analoghifi/Thel-VX-preamp/VX-D/docs/german/VXDNF.png

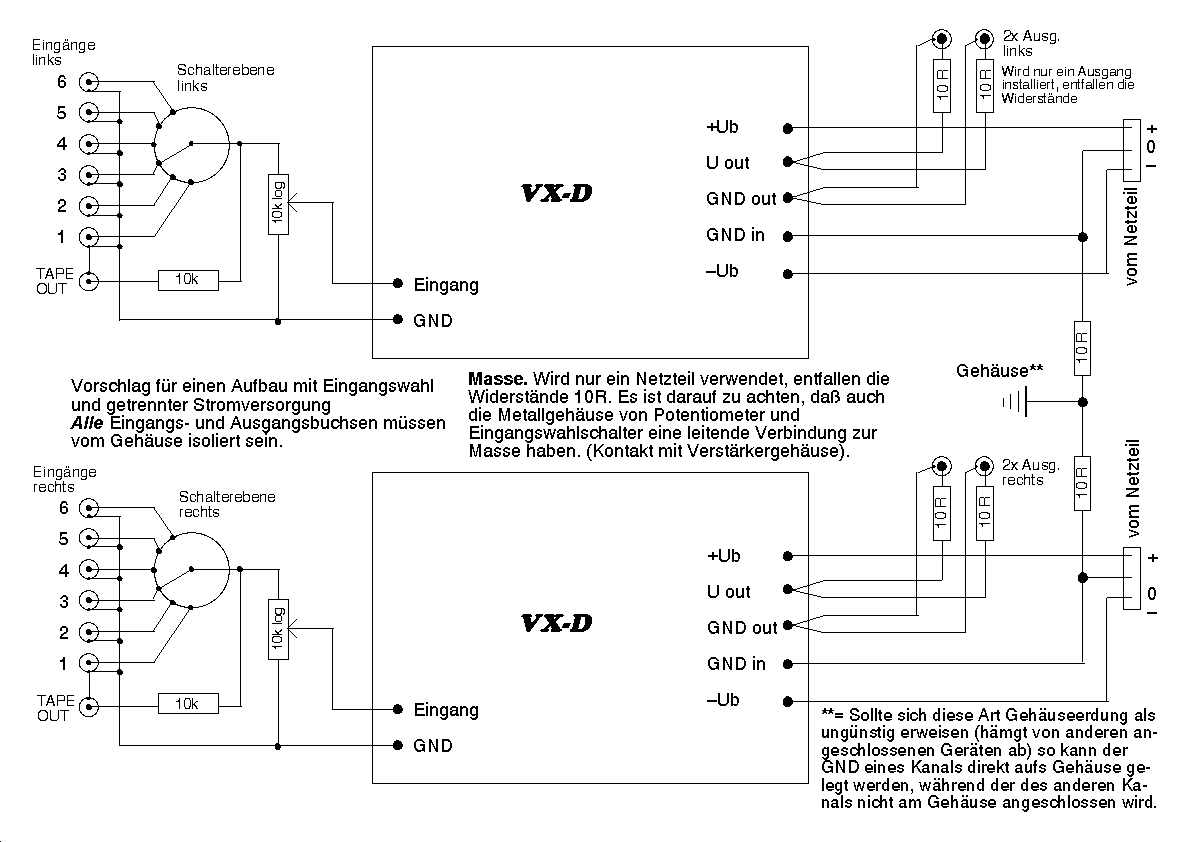
VX-D/docs/german/VXDNF.png
