analoghifi/Thel-VX-preamp/VX-D/hardware/VX-D_2.jpg

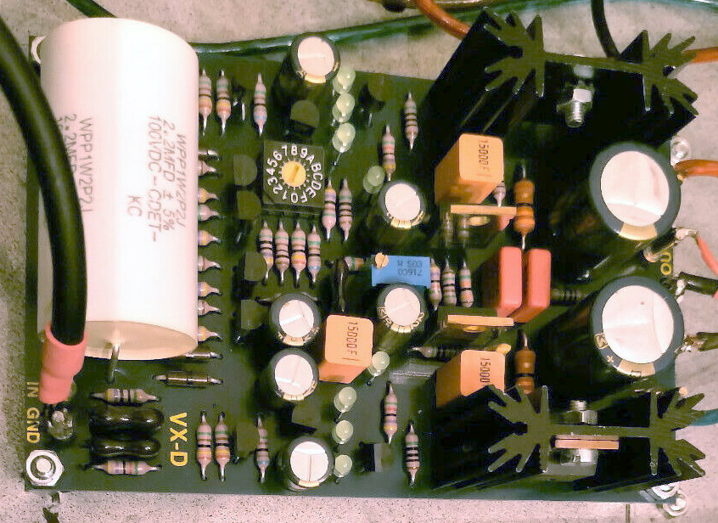
VX-D/hardware/VX-D_2.jpg
