analoghifi/Thel-VX-preamp/VX-D/hardware/VX-D_later_exemplar_1.jpg

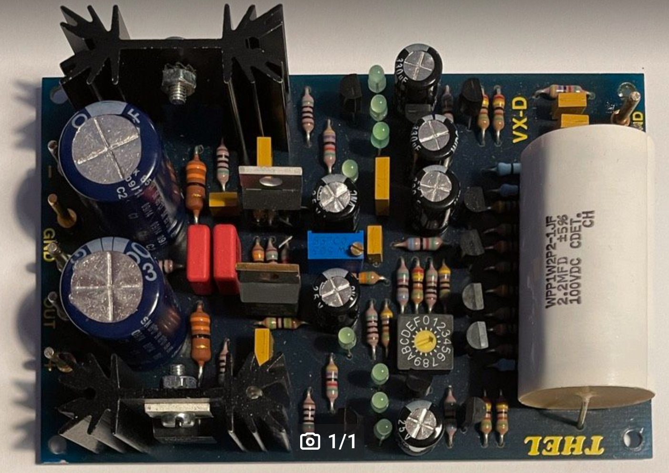
VX-D/hardware/VX-D_later_exemplar_1.jpg
