analoghifi/Thel-VX-preamp/VX-D/hardware/VX-D_later_exemplar_2.jpg

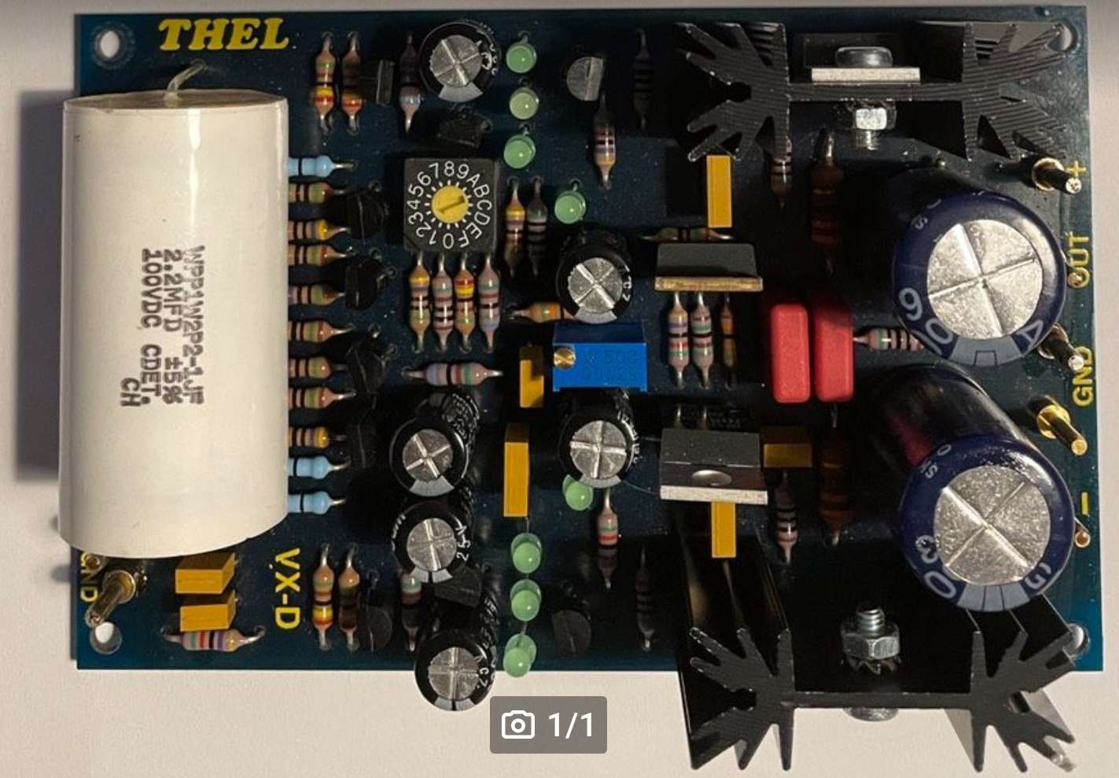
VX-D/hardware/VX-D_later_exemplar_2.jpg
