analoghifi/Thel-VX-preamp/VX-D/hardware/VX-D_Schematic_corr.jpg

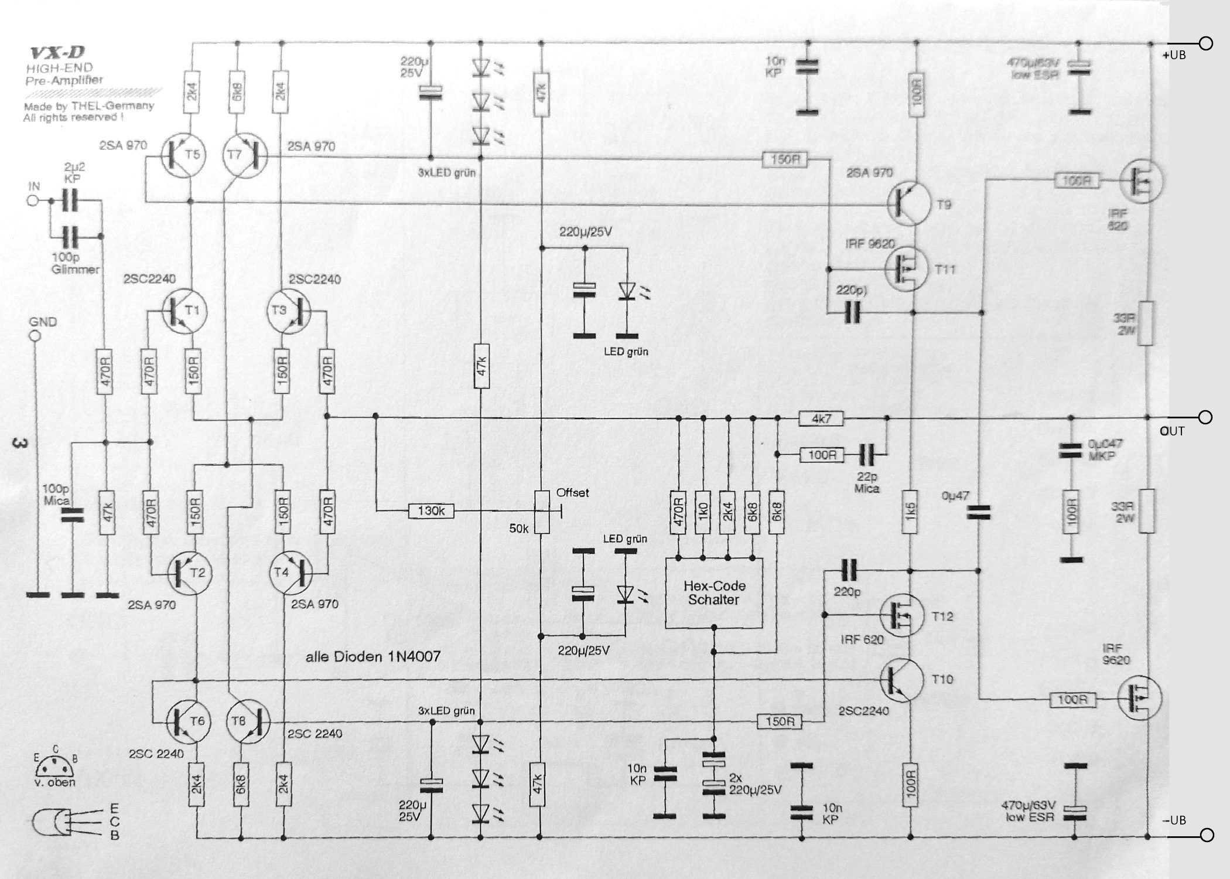
VX-D/hardware/VX-D_Schematic_corr.jpg
