analoghifi/Thel-VX-preamp/VX-Line/docs/german/VX-L1.png

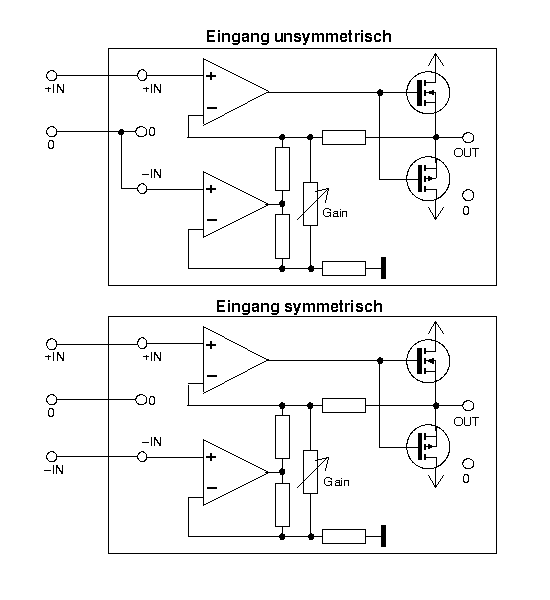
VX-Line/docs/german/VX-L1.png
