analoghifi/Thel-VX-preamp/VX-Line/docs/german/VX-L2.png

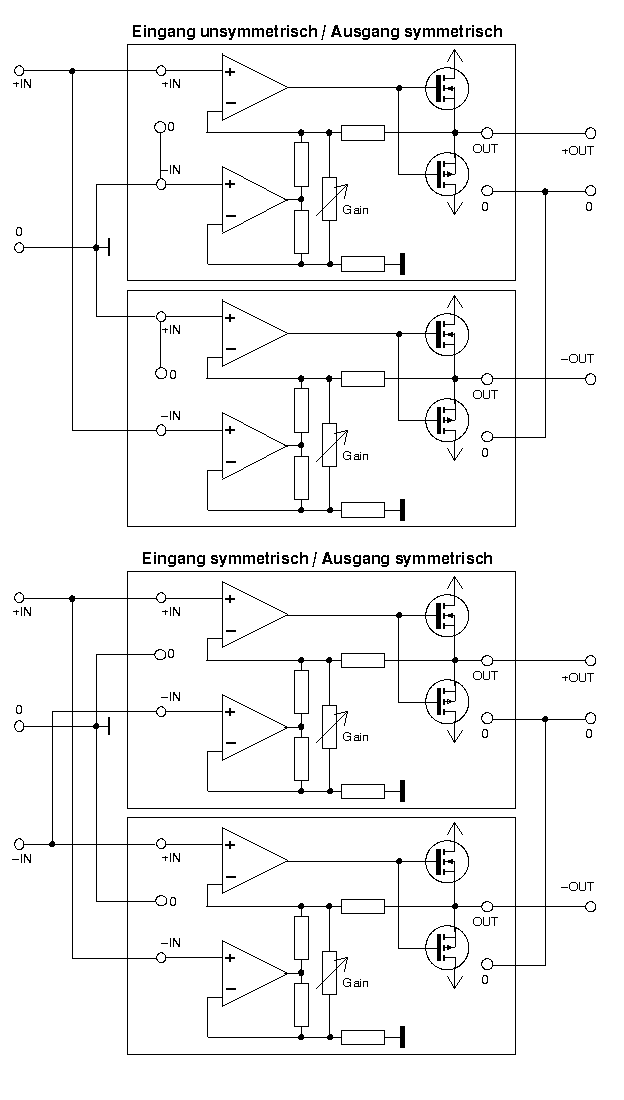
VX-Line/docs/german/VX-L2.png
