analoghifi/Thel-VX-preamp/VX-Line/hardware/KiCad/VX-Line_2021__original/VX-Line_original_1Layer_THT.sch.png

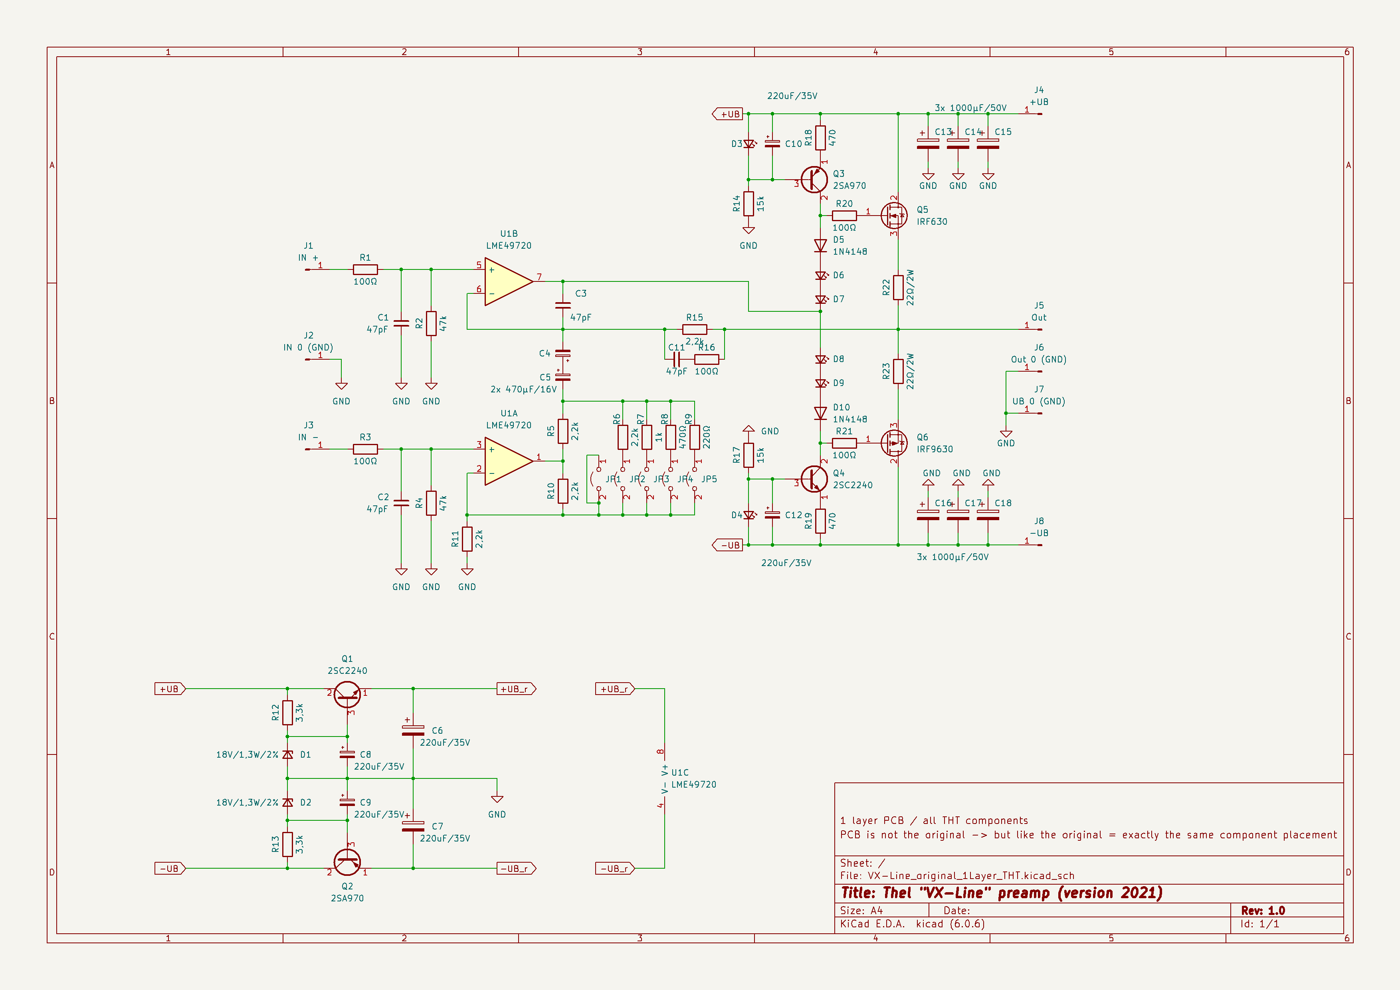
VX-Line/hardware/KiCad/VX-Line_2021__original/VX-Line_original_1Layer_THT.sch.png
