analoghifi/Thel-VX-preamp/VX-Line/hardware/KiCad/VX-Line_2021__original/VX-Line_original_1Layer_THT__3D_2.png

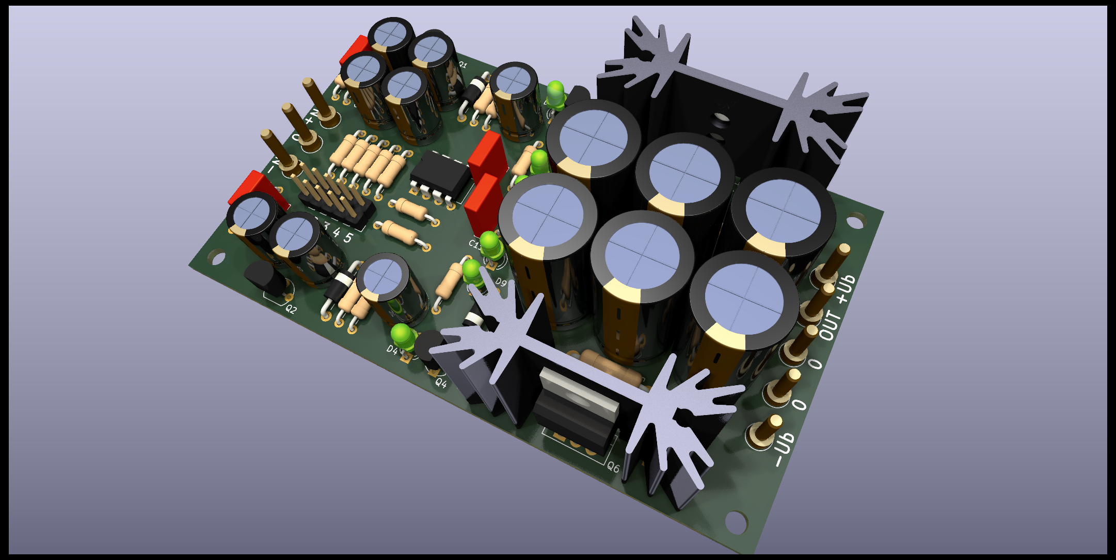
VX-Line/hardware/KiCad/VX-Line_2021__original/VX-Line_original_1Layer_THT__3D_2.png
