analoghifi/Thel-VX-preamp/VX-Line/hardware/VX-Line_2017-2020.jpg

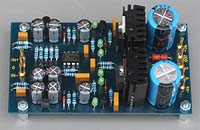
VX-Line/hardware/VX-Line_2017-2020.jpg
