analoghifi/Thel-VX-preamp/VX-Line/hardware/VX-Line_2021-PCB_Bottom.jpg

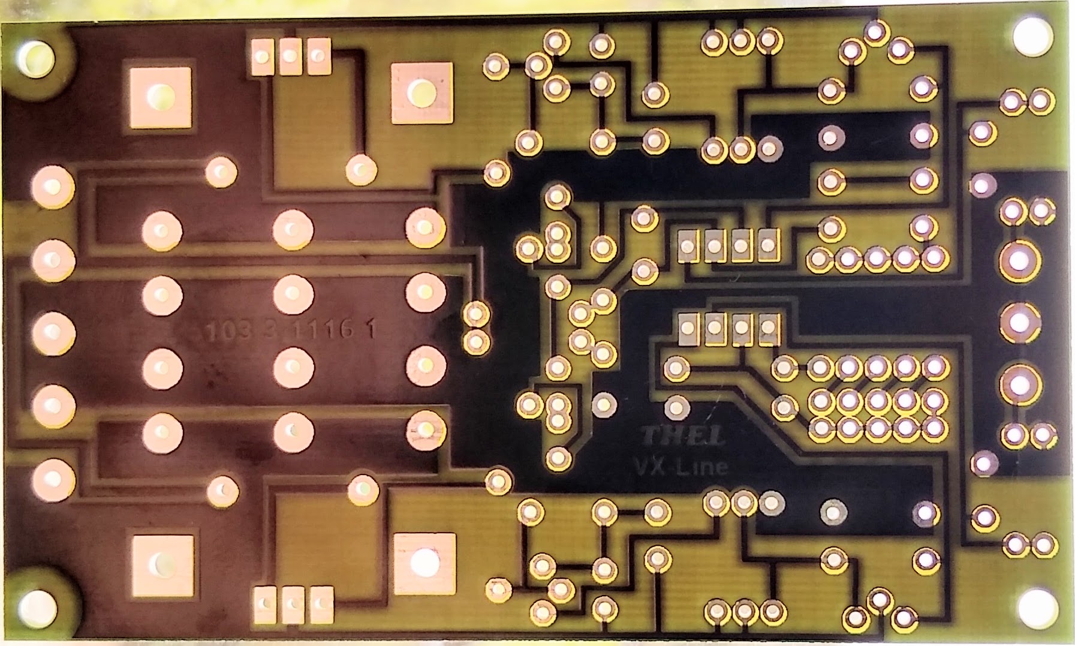
VX-Line/hardware/VX-Line_2021-PCB_Bottom.jpg
